herraa1/msx-tidesrider-enclosure-v1/images/msx-tidesrider-enclosure-v1-bottom-overview-IMG_7867.png

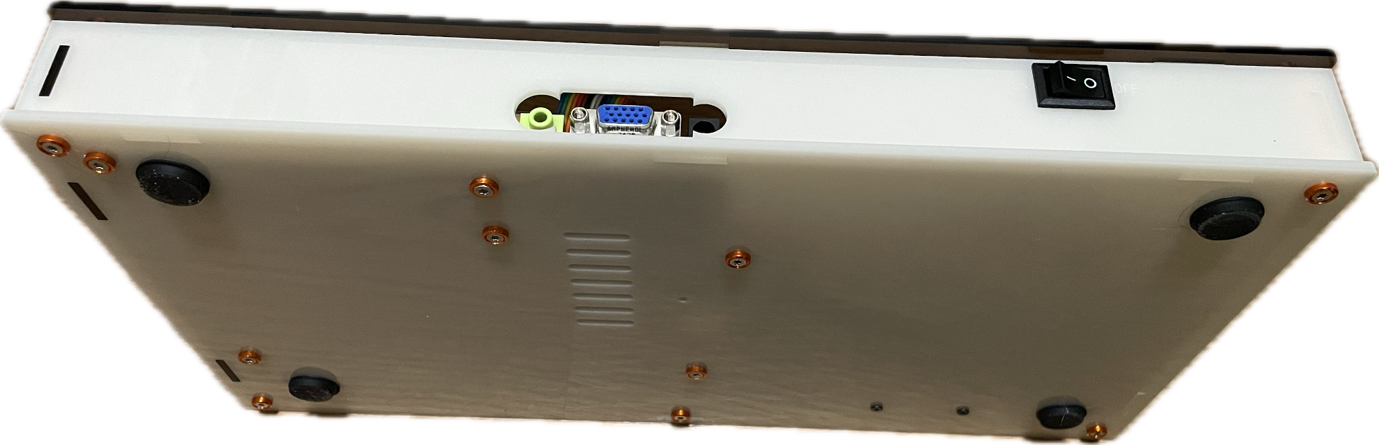
images/msx-tidesrider-enclosure-v1-bottom-overview-IMG_7867.png
